dfdtc/IC_705_CNC_Shield/Accessories/2040铝角码.STEP

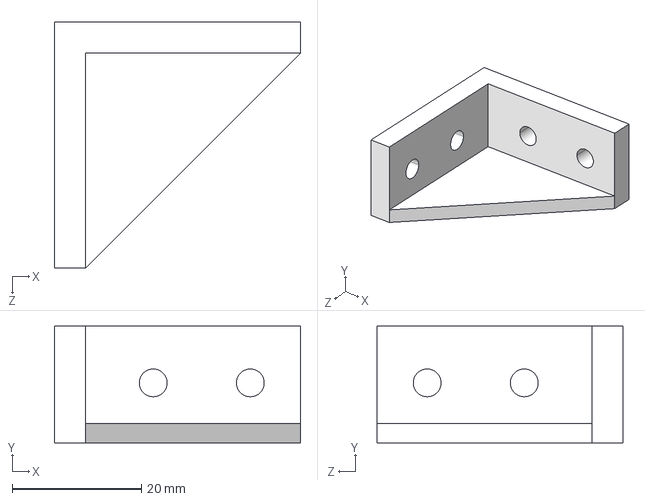
[picture p15: CAD file, 2025-08-10]
Accessories/2040铝角码.STEP
38.0 x 18.0 x 38.0 mm
