dfdtc/IC_705_CNC_Shield/BasePlate/底板_开快装板螺纹底孔.STEP

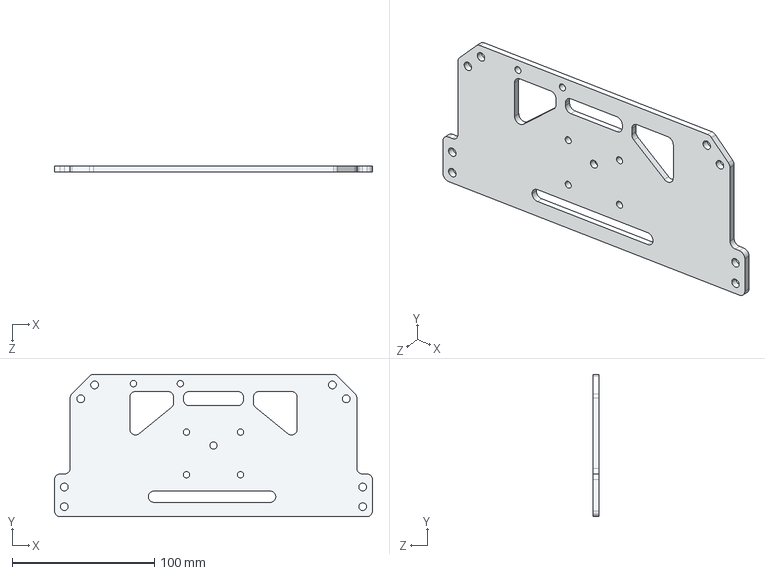
[picture p16: CAD file, 2025-08-10]
BasePlate/底板_开快装板螺纹底孔.STEP
223.6 x 100.0 x 4.00 mm
